skeatz/FabPDI/images/fabpdi-mega8_outline.png

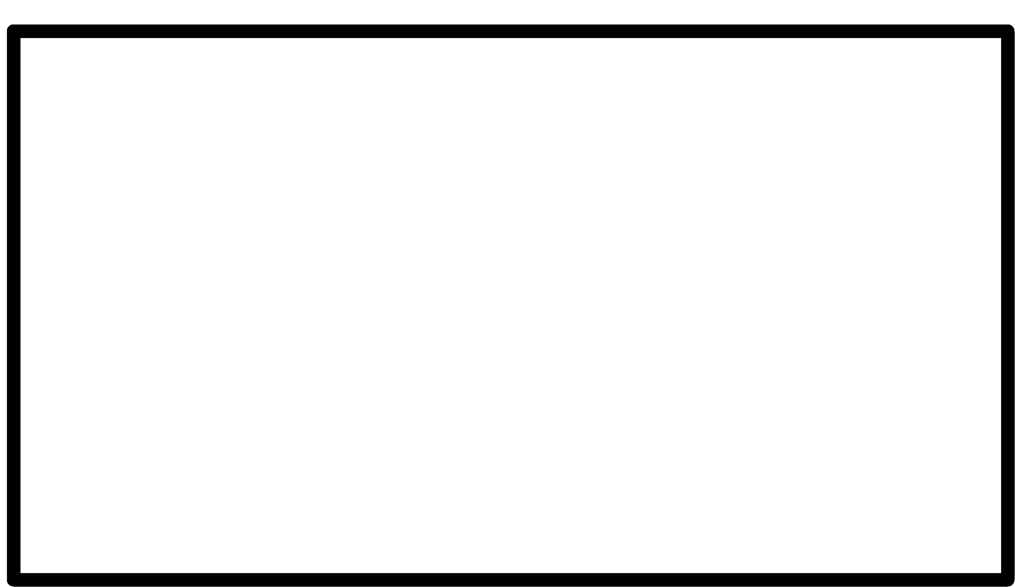
images/fabpdi-mega8_outline.png
